abe-frickelbude/passat-dashboard-mod/adc-serial-monitor/src/main/java/de/fb/arduino_sandbox/service/firmata/FirmataUplink.java

package de.fb.arduino_sandbox.service.firmata;

import java.util.Arrays;
import java.util.Collections;
import java.util.HashMap;
import java.util.List;
import java.util.Map;
import java.util.function.Consumer;
import javax.annotation.PreDestroy;
import org.apache.commons.lang3.ArrayUtils;
import org.slf4j.Logger;
import org.slf4j.LoggerFactory;
import org.springframework.beans.factory.annotation.Value;
import org.springframework.stereotype.Service;
import com.bortbort.arduino.FiloFirmata.Firmata;
import com.bortbort.arduino.FiloFirmata.FirmataConfiguration;
import com.bortbort.arduino.FiloFirmata.MessageListener;
import com.bortbort.arduino.FiloFirmata.Messages.AnalogMessage;
import de.fb.arduino_sandbox.model.RgbwPixel;
import de.fb.arduino_sandbox.service.HardwareUplink;
import de.fb.arduino_sandbox.util.Constants;
import de.fb.arduino_sandbox.view.SerialPortParams;
import jssc.SerialPortList;

/**
 * 
 * @author Ibragim Kuliev
 *
 */
@Service
public class FirmataUplink implements HardwareUplink {

    private static final Logger log = LoggerFactory.getLogger(FirmataUplink.class);

    private Firmata firmataLink;

    private final Map<Integer, Consumer<Integer>> adcSampleConsumers;
    private final Map<Integer, MessageListener<FbAnalogMessage>> adcMessageListeners;

    @Value("${arduino.connect.ping}")
    private Boolean pingProbe;

    @Value("${arduino.connect.timeout}")
    private Integer waitTimeout;

    static {
        Firmata.addCustomCommandParser(new FbAnalogMessageBuilder());
    }

    public FirmataUplink() {
        adcSampleConsumers = new HashMap<>();
        adcMessageListeners = new HashMap<>();
    }

    @Override
    public List<String> getAvailablePorts() {

        List<String> portNames = Collections.emptyList();
        try {
            String[] names = SerialPortList.getPortNames();
            if (ArrayUtils.isNotEmpty(names)) {
                portNames = Arrays.asList(names);
            }
        } catch (Exception ex) {
            log.warn("Cannot enumerate serial ports!", ex);
        }
        return portNames;
    }

    @Override
    public void connect(final SerialPortParams params) {

        log.info("Initializing Firmata on {} with {} baud...", params.getPortName(), params.getBaudRate());

        final FirmataConfiguration config = new FirmataConfiguration();
        config.setTestProtocolCommunication(pingProbe);
        config.setSerialPortID(params.getPortName());
        config.setSerialPortBaudRate(params.getBaudRate());

        firmataLink = new Firmata(config);
        boolean startedOk = firmataLink.start();
        if (!startedOk) {
            // TODO: exception
        }
        log.info("Connected!");
    }

    @Override
    public void disconnect() {
        if (firmataLink != null && firmataLink.getStarted()) {
            try {
                firmataLink.stop();
            } catch (Exception ex) {
                log.error("Cannot close serial link!");
            }
        }
    }

    @Override
    public void setAdcSampleConsumer(final Integer pin, final Consumer<Integer> consumer) {
        adcSampleConsumers.put(pin, consumer);
        addAdcMessageListener(pin, consumer);
    }

    @Override
    public void removeAdcSampleConsumer(final Integer pin) {
        if (adcSampleConsumers.containsKey(pin)) {
            adcSampleConsumers.remove(pin);
            removeAdcMessageListener(pin);
        }
    }

    @Override
    public void startListening(final Integer pin) {
        if (firmataLink != null && firmataLink.getStarted()) {
            firmataLink.addMessageListener(adcMessageListeners.get(pin));
        }
    }

    @Override
    public void stopListening(final Integer pin) {
        if (firmataLink != null && firmataLink.getStarted() && adcMessageListeners.containsKey(pin)) {
            firmataLink.removeMessageListener(adcMessageListeners.get(pin));
        }
    }

    @Override
    public void stopAll() {
        for (int pin : Constants.ANALOG_PINS) {
            stopListening(pin);
        }
    }

    @Override
    public void resetPixels() {
        if (firmataLink != null && firmataLink.getStarted()) {
            // clear out previous LED strip configuration
            firmataLink.sendMessage(new ResetPixelsCommand());
        }
    }

    @Override
    public void sendRgbwPixels(final List<RgbwPixel> pixels) {

        if (firmataLink != null && firmataLink.getStarted()) {

            // supply the correct number of pixels to use (important on the firmware side !!)
            firmataLink.sendMessage(new SetNumPixelsCommand(pixels.size()));

            for (int index = 0; index < pixels.size(); index++) {

                final RgbwPixel pixel = pixels.get(index);
                SetPixelCommand pixelMessage = new SetPixelCommand(index,
                    pixel.getRed(), pixel.getGreen(), pixel.getBlue(),
                    pixel.getWhite());

                firmataLink.sendMessage(pixelMessage);
            }

            firmataLink.sendMessage(new ShowPixelsCommand());
        }
    }

    @PreDestroy
    private void cleanUp() {
        // stopAll();
        disconnect();
        adcSampleConsumers.clear();
    }

    private void addAdcMessageListener(final Integer pin, final Consumer<Integer> consumer) {

        /**
         * Note: MessageListener.from() methods will not work with Java > 8 due to obsolete transient
         * dependencies, hence the local anonymous class!
         */
        final MessageListener<FbAnalogMessage> listener = new MessageListener<>(pin) {

            @Override
            public void messageReceived(final FbAnalogMessage message) {
                consumer.accept(Integer.valueOf(message.getAnalogValue()));
            }
        };

        adcMessageListeners.put(pin, listener);
    }

    private void removeAdcMessageListener(final Integer pin) {
        firmataLink.removeMessageListener(adcMessageListeners.get(pin));
        adcMessageListeners.remove(pin);
    }
}
