abe-frickelbude/passat-dashboard-mod/adc-serial-monitor/src/main/java/de/fb/arduino_sandbox/view/component/color/RgbwSwatchGroup.java

package de.fb.arduino_sandbox.view.component.color;

import java.awt.Color;
import java.awt.Dimension;
import java.awt.Font;
import java.util.ArrayList;
import java.util.Collections;
import java.util.List;
import java.util.function.Consumer;
import javax.swing.JComponent;
import javax.swing.JSpinner;
import javax.swing.SpinnerNumberModel;
import org.apache.commons.collections4.CollectionUtils;
import org.kordamp.ikonli.octicons.Octicons;
import org.kordamp.ikonli.swing.FontIcon;
import com.jgoodies.forms.layout.ColumnSpec;
import com.jgoodies.forms.layout.FormLayout;
import com.jgoodies.forms.layout.FormSpecs;
import com.jgoodies.forms.layout.RowSpec;
import de.fb.arduino_sandbox.view.component.color_swatch.ColorSwatch;
import de.fb.arduino_sandbox.view.component.dial.Dial;

final class RgbwSwatchGroup extends JComponent {

    private static final Font FONT = new Font("Dialog", Font.PLAIN, 9);
    private static final Dimension SWATCH_SIZE = new Dimension(32, 32);
    private static final Dimension DIAL_SIZE = new Dimension(40, 40);

    private final ColorSwatch colorSwatch;
    private final Dial luminanceDial;
    private final JSpinner groupSizeSpinner;
    private final TinyButtonGroup plusMinusButtons;

    private List<Consumer<RgbwColorGroup>> changeCallbacks;

    private RgbwSwatchGroup() {

        super();
        changeCallbacks = Collections.emptyList();

        colorSwatch = new ColorSwatch();
        colorSwatch.setBorderEnabled(true);
        colorSwatch.setColor(Color.BLACK);

        colorSwatch.setPreferredSize(SWATCH_SIZE);
        colorSwatch.setMinimumSize(SWATCH_SIZE);
        colorSwatch.setMaximumSize(SWATCH_SIZE);

        luminanceDial = new Dial();
        luminanceDial.setMin(0);
        luminanceDial.setMax(255);
        luminanceDial.setCoarseStep(20);
        luminanceDial.setFineStep(1);

        luminanceDial.setPreferredSize(DIAL_SIZE);
        luminanceDial.setMinimumSize(DIAL_SIZE);
        luminanceDial.setMaximumSize(DIAL_SIZE);

        groupSizeSpinner = new JSpinner();
        SpinnerNumberModel model = new SpinnerNumberModel(1, 1, 999, 1);
        groupSizeSpinner.setModel(model);
        groupSizeSpinner.setFont(FONT);

        plusMinusButtons = new TinyButtonGroup();
        plusMinusButtons.addButton(FontIcon.of(Octicons.DASH));
        plusMinusButtons.addButton(FontIcon.of(Octicons.PLUS));

        initLayout();
        registerEvents();
    }

    private void initLayout() {

        final FormLayout layout = new FormLayout(
            new ColumnSpec[] {
                FormSpecs.RELATED_GAP_COLSPEC,
                ColumnSpec.decode("48px")
            },
            new RowSpec[] {
                FormSpecs.RELATED_GAP_ROWSPEC,
                RowSpec.decode("48px"), // color swatch
                FormSpecs.RELATED_GAP_ROWSPEC,
                RowSpec.decode("48px"), // white swatch
                FormSpecs.RELATED_GAP_ROWSPEC,
                FormSpecs.DEFAULT_ROWSPEC, // count spinner
                FormSpecs.RELATED_GAP_ROWSPEC,
                FormSpecs.DEFAULT_ROWSPEC, // remove button
                FormSpecs.RELATED_GAP_ROWSPEC
            });

        this.setLayout(layout);

        // note: stuff always added to EVEN columns and EVEN rows, as the ODD ones contain the gaps
        // row 2 - color swatch
        // row 4 - white swatch
        // row 6 - spinner
        // row 8 - remove button
        this.add(colorSwatch, "2,2,fill,fill");
        this.add(luminanceDial, "2,4,center,fill");
        this.add(groupSizeSpinner, "2,6,fill,fill");
        this.add(plusMinusButtons, "2,8,center,center");
    }

    public static RgbwSwatchGroup create() {
        return new RgbwSwatchGroup();
    }

    public TinyButtonGroup getPlusMinusButtons() {
        return plusMinusButtons;
    }

    public Color getColor() {
        return colorSwatch.getColor();
    }

    public void setColor(final Color color) {
        colorSwatch.setColor(color);
    }

    public int getWhite() {
        return luminanceDial.getValue();
    }

    public void setWhite(final int whiteLevel) {
        if (whiteLevel < 0 || whiteLevel > 255) {
            throw new IllegalArgumentException("White level out of range! (0 - 255)");
        }
        luminanceDial.setValue(whiteLevel);
    }

    public int getGroupSize() {
        return Integer.class.cast(groupSizeSpinner.getValue());
    }

    public void setGroupSize(final int groupSize) {
        groupSizeSpinner.setValue(groupSize);
    }

    public void setMinusEnabled(final boolean enabled) {
        plusMinusButtons.getButton(0).setEnabled(enabled);
    }

    public void setPlusEnabled(final boolean enabled) {
        plusMinusButtons.getButton(1).setEnabled(enabled);
    }

    public void addChangeCallback(final Consumer<RgbwColorGroup> callback) {
        if (CollectionUtils.isEmpty(changeCallbacks)) {
            changeCallbacks = new ArrayList<>();
        }
        changeCallbacks.add(callback);
    }

    public void registerRemoveCallback(final Consumer<RgbwSwatchGroup> callback) {
        plusMinusButtons.getButton(0).addActionCallback(() -> {
            callback.accept(this);
        });
    }

    public void registerAddCallback(final Consumer<RgbwSwatchGroup> callback) {
        plusMinusButtons.getButton(1).addActionCallback(() -> {
            callback.accept(this);
        });
    }

    private void registerEvents() {
        colorSwatch.addChangeListener(event -> fireChangeEvent());
        luminanceDial.addChangeListener(event -> fireChangeEvent());
        groupSizeSpinner.addChangeListener(event -> fireChangeEvent());
    }

    private void fireChangeEvent() {
        final RgbwColorGroup colorGroup = new RgbwColorGroup(getColor(), getWhite(), getGroupSize());
        for (final Consumer<RgbwColorGroup> callback : changeCallbacks) {
            callback.accept(colorGroup);
        }
    }
}
